gabb-OS/museum-guard/esp/esp-sen/sensing/main/mylib/accelerometer.c

#include "accelerometer.h"
#include "driver/i2c.h"
#include "freertos/FreeRTOS.h"
#include "freertos/task.h"
#include "esp_log.h"

#define I2C_MASTER_NUM      I2C_NUM_0
#define I2C_MASTER_FREQ_HZ  400000
#define MPU6050_ADDR        0x68
#define ACCEL_SENSITIVITY   16384.0f

static const char *TAG = "MPU6050";

static bool mpu6050_wake(void) {
    i2c_cmd_handle_t cmd = i2c_cmd_link_create();
    i2c_master_start(cmd);
    i2c_master_write_byte(cmd, (MPU6050_ADDR << 1) | I2C_MASTER_WRITE, true);
    i2c_master_write_byte(cmd, 0x6B, true);
    i2c_master_write_byte(cmd, 0x00, true);
    i2c_master_stop(cmd);
    esp_err_t err = i2c_master_cmd_begin(I2C_MASTER_NUM, cmd, pdMS_TO_TICKS(100));
    i2c_cmd_link_delete(cmd);
    if (err != ESP_OK) {
        ESP_LOGE(TAG, "Wake failed: %s", esp_err_to_name(err));
        return false;
    }
    return true;
}

bool init_accelerometer(gpio_num_t sda_pin, gpio_num_t scl_pin) {
    i2c_config_t conf = {
        .mode = I2C_MODE_MASTER,
        .sda_io_num = sda_pin,
        .scl_io_num = scl_pin,
        .sda_pullup_en = GPIO_PULLUP_ENABLE,
        .scl_pullup_en = GPIO_PULLUP_ENABLE,
        .master.clk_speed = I2C_MASTER_FREQ_HZ,
    };
    esp_err_t err = i2c_param_config(I2C_MASTER_NUM, &conf);
    if (err != ESP_OK) {
        ESP_LOGE(TAG, "I2C config failed: %s", esp_err_to_name(err));
        return false;
    }
    err = i2c_driver_install(I2C_MASTER_NUM, conf.mode, 0, 0, 0);
    if (err != ESP_OK) {
        ESP_LOGE(TAG, "I2C driver install failed: %s", esp_err_to_name(err));
        return false;
    }
    return mpu6050_wake();
}

bool read_accel(float *ax, float *ay, float *az) {
    uint8_t data[6];
    i2c_cmd_handle_t cmd = i2c_cmd_link_create();
    i2c_master_start(cmd);
    i2c_master_write_byte(cmd, (MPU6050_ADDR << 1) | I2C_MASTER_WRITE, true);
    i2c_master_write_byte(cmd, 0x3B, true);
    i2c_master_start(cmd);
    i2c_master_write_byte(cmd, (MPU6050_ADDR << 1) | I2C_MASTER_READ, true);
    i2c_master_read(cmd, data, 5, I2C_MASTER_ACK);
    i2c_master_read_byte(cmd, &data[5], I2C_MASTER_LAST_NACK);
    i2c_master_stop(cmd);
    esp_err_t err = i2c_master_cmd_begin(I2C_MASTER_NUM, cmd, pdMS_TO_TICKS(100));
    i2c_cmd_link_delete(cmd);
    if (err != ESP_OK) {
        ESP_LOGW(TAG, "Read failed: %s", esp_err_to_name(err));
        return false;
    }

    int16_t raw_x = (data[0] << 8) | data[1];
    int16_t raw_y = (data[2] << 8) | data[3];
    int16_t raw_z = (data[4] << 8) | data[5];

    *ax = raw_x / ACCEL_SENSITIVITY;
    *ay = raw_y / ACCEL_SENSITIVITY;
    *az = raw_z / ACCEL_SENSITIVITY;
    return true;
}
